DAlexis/gps-timestamper/c-sources/gps-timestamper/high-level/include/gps-timestamper.hpp

/*
 * gps-timestamper.hpp
 *
 *  Created on: 6 дек. 2016 г.
 *      Author: dalexies
 */

#ifndef HIGH_LEVEL_INCLUDE_GPS_TIMESTAMPER_HPP_
#define HIGH_LEVEL_INCLUDE_GPS_TIMESTAMPER_HPP_

#include "macro.hpp"
#include "nmea-receiver.hpp"
#include "precision-timer.hpp"
#include "timestamp-collector.hpp"
#include "output-maker.hpp"
#include "time-location-manager.hpp"
#include "treshold-controller.hpp"
#include "leds.hpp"

extern UART_HandleTypeDef huart3;
extern TIM_HandleTypeDef htim2;
extern DAC_HandleTypeDef hdac;

class GPSTimestamper
{
public:
	void run();

	SINGLETON_IN_CLASS(GPSTimestamper)

private:
	GPSTimestamper();

	NMEAReceiver m_nmea{&huart3};
	OutputMaker m_outputMaker;
	PrecisionTimer m_precTimer{&htim2, m_outputMaker};

	TimeLocationManager m_timeLocMgr{m_nmea, m_precTimer, m_outputMaker};
	TimestampCollector m_collector{m_timeLocMgr, &m_precTimer, m_outputMaker};
    ThresholdController m_tresholdController{&hdac};
    Leds m_leds;
};

#endif /* HIGH_LEVEL_INCLUDE_GPS_TIMESTAMPER_HPP_ */
