DAlexis/gps-timestamper/c-sources/gps-timestamper/high-level/include/gps-timestamper-entry-point.h

/*
 * gps-timestamper-entry-point.h
 *
 *  Created on: 6 дек. 2016 г.
 *      Author: dalexies
 */

#ifndef HIGH_LEVEL_INCLUDE_GPS_TIMESTAMPER_ENTRY_POINT_H_
#define HIGH_LEVEL_INCLUDE_GPS_TIMESTAMPER_ENTRY_POINT_H_

#ifdef __cplusplus
	extern "C" {
#endif

void entryPoint(void);

#ifdef __cplusplus
	}
#endif


#endif /* HIGH_LEVEL_INCLUDE_GPS_TIMESTAMPER_ENTRY_POINT_H_ */
