DAlexis/gps-timestamper/c-sources/gps-timestamper/high-level/include/precision-timer.hpp

/*
 * precision-timer.hpp
 *
 *  Created on: 6 дек. 2016 г.
 *      Author: dalexies
 */

#ifndef GPS_TIMESTAMPER_HIGH_LEVEL_INCLUDE_PRECISION_TIMER_HPP_
#define GPS_TIMESTAMPER_HIGH_LEVEL_INCLUDE_PRECISION_TIMER_HPP_

#include "output-messages.hpp"
#include "stm32f4xx_hal.h"

#include <functional>
#include <stdint.h>

class PrecisionTimer
{
public:
    using IRQSignalCaptureCallback = std::function<void(bool hasTiming, uint32_t oneSecPeriod, uint32_t signalDelay)>;
	using IRQPPSCaptureCallback = std::function<void()>;

	enum class CaptureSource {
        PPS, signal
	};

	PrecisionTimer(TIM_HandleTypeDef* htim, IOutputMessagesReceiver& outputReceiver);
	void run();
	/// This function should be called regulary to ensure that we have valid last GPS records
	void checkForGPSDisconnect();
	uint32_t getValue();
	void setCaptureCallback(IRQSignalCaptureCallback callback);
	void setPPSCaptureCallback(IRQPPSCaptureCallback callback);

	void captureIRQHandler(CaptureSource source, uint32_t value);
	const TIM_HandleTypeDef* timerHandler();


private:
	TIM_HandleTypeDef* m_htim;
	IOutputMessagesReceiver& m_outputReceiver;
	uint32_t m_prevGPS = 0;
	uint32_t m_lastGPS = 0;
	uint32_t m_gpsCount = 0;

	IRQSignalCaptureCallback m_signalCallback = nullptr;
	IRQPPSCaptureCallback m_ppsCallback = nullptr;
};

class OutputGPSDisconnect : public IOutputMessage
{
public:
    std::string str() const override;
private:
};


#endif /* GPS_TIMESTAMPER_HIGH_LEVEL_INCLUDE_PRECISION_TIMER_HPP_ */
