DAlexis/gps-timestamper/c-sources/gps-timestamper/high-level/include/macro.hpp

/*
*    Copyright (C) 2016 by Aleksey Bulatov
*
*    This file is part of Caustic Lasertag System project.
*
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
*    @license GPL-3.0+ <http://spdx.org/licenses/GPL-3.0+>
*/

#ifndef LAZERTAG_RIFLE_INCLUDE_CORE_MACRO_UTILS_HPP_
#define LAZERTAG_RIFLE_INCLUDE_CORE_MACRO_UTILS_HPP_

#define STRINGIFICATE(a)    _STRINGIFICATE(a)
#define _STRINGIFICATE(a)   #a

#define ARRAY_SIZE(a)       (sizeof(a) / sizeof(a[0]))

#define SINGLETON_IN_CPP(ClassName)		ClassName& ClassName::instance() \
										{ \
												static ClassName singletonInstance; \
												return singletonInstance; \
										}


#define SINGLETON_IN_CLASS(ClassName)	static ClassName& instance(); \
										ClassName(const ClassName&) = delete;

#define ADD_BITS(where, what)		(where) |= (what)
#define REMOVE_BITS(where, what)	(where) &= ~(what)

#define UNUSED_ARG(x)		( (void) x )

#endif /* LAZERTAG_RIFLE_INCLUDE_CORE_MACRO_UTILS_HPP_ */
