DAlexis/gps-timestamper/c-sources/gps-timestamper/high-level/include/tests.hpp

/*
 * tests.hpp
 *
 *  Created on: 13 апр. 2017 г.
 *      Author: dalexies
 */

#ifndef GPS_TIMESTAMPER_HIGH_LEVEL_INCLUDE_TESTS_HPP_
#define GPS_TIMESTAMPER_HIGH_LEVEL_INCLUDE_TESTS_HPP_

#include "output-messages.hpp"

class QueueOverflowTest
{
public:
	void run();
};


#endif /* GPS_TIMESTAMPER_HIGH_LEVEL_INCLUDE_TESTS_HPP_ */
